arkorobotics/OneButton/Hardware/CAD/CAPC-0603-T0.9-BN.stp

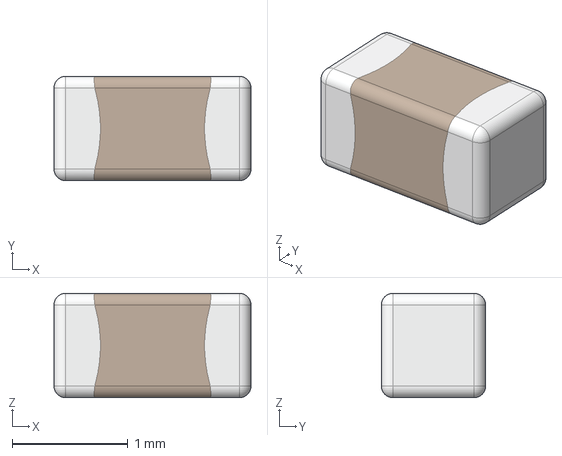
[picture p21: CAD file, 2017-11-20]
Hardware/CAD/CAPC-0603-T0.9-BN.stp
1.70 x 0.9 x 0.9 mm
