arkorobotics/OneButton/Hardware/CAD/MO-178AA.stp

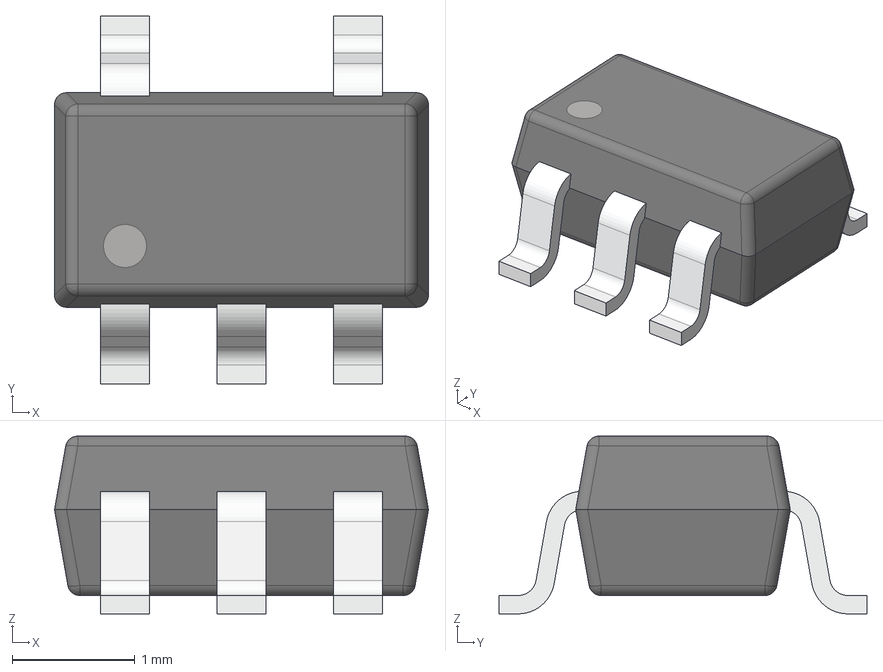
[picture p22: CAD file, 2017-11-20]
Hardware/CAD/MO-178AA.stp
3.05 x 3.00 x 1.45 mm
