arkorobotics/OneButton/Hardware/CAD/CAPC-1210-T1.8-BN.stp

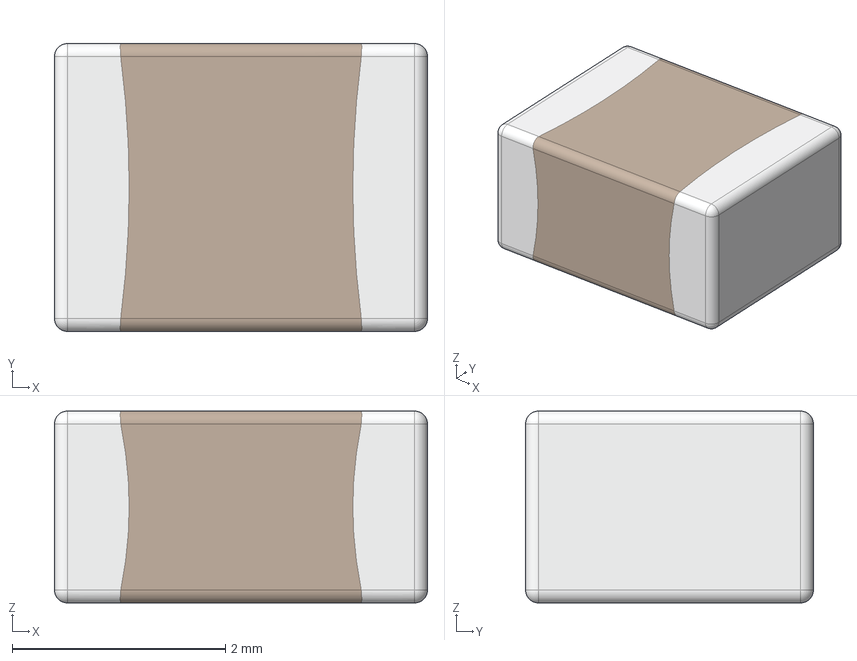
[picture p23: CAD file, 2017-11-20]
Hardware/CAD/CAPC-1210-T1.8-BN.stp
3.50 x 2.70 x 1.80 mm
