arkorobotics/OneButton/Hardware/CAD/SOT223.STEP

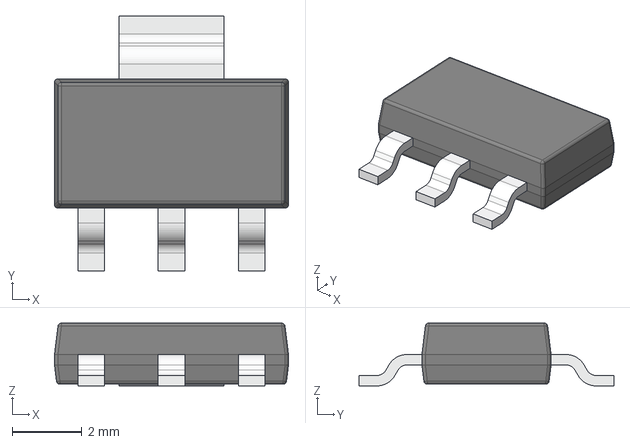
[picture p24: CAD file, 2017-11-20]
Hardware/CAD/SOT223.STEP
6.70 x 7.30 x 1.80 mm
