arkorobotics/OneButton/Hardware/CAD/SC-76.stp

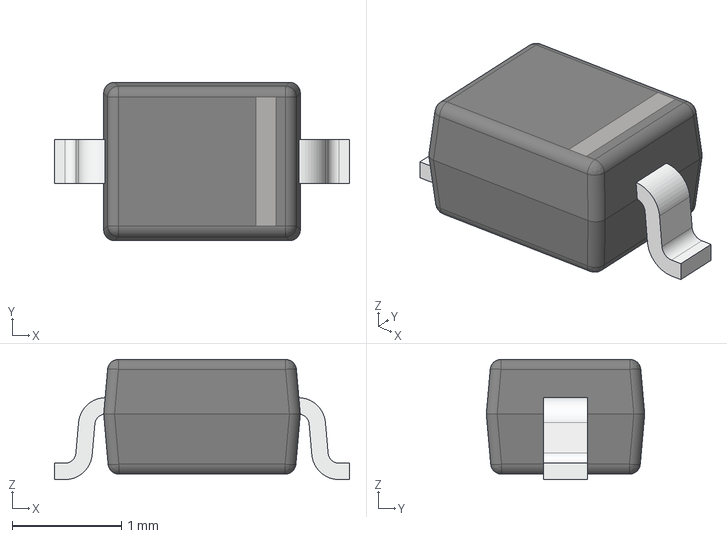
[picture p25: CAD file, 2017-11-20]
Hardware/CAD/SC-76.stp
2.70 x 1.45 x 1.10 mm
