arkorobotics/OneButton/Hardware/CAD/CAPC-1206-T1.8-BN.stp

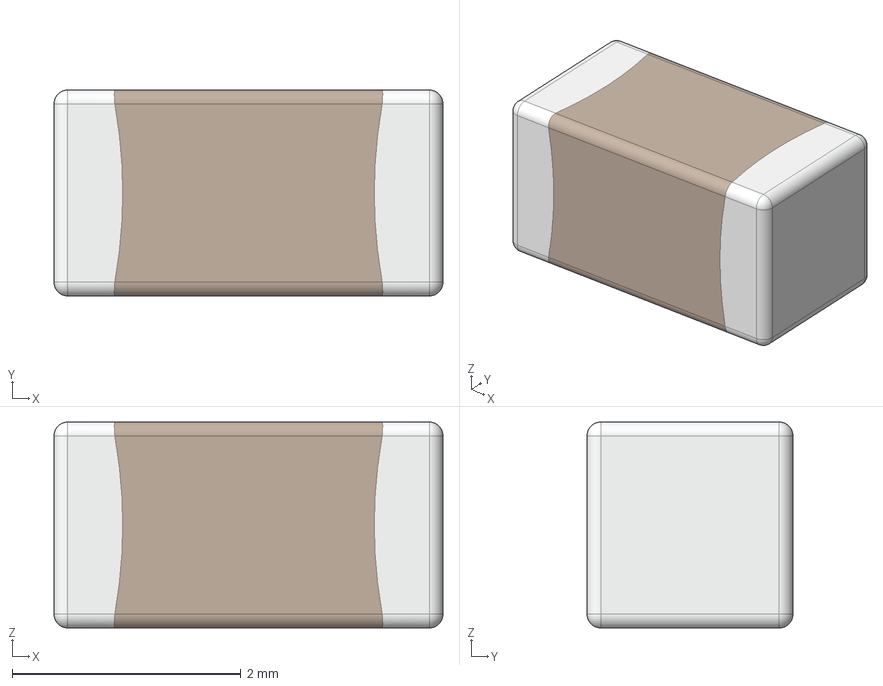
[picture p26: CAD file, 2017-11-20]
Hardware/CAD/CAPC-1206-T1.8-BN.stp
3.40 x 1.80 x 1.80 mm
