arkorobotics/OneButton/Hardware/CAD/Crystal.STEP

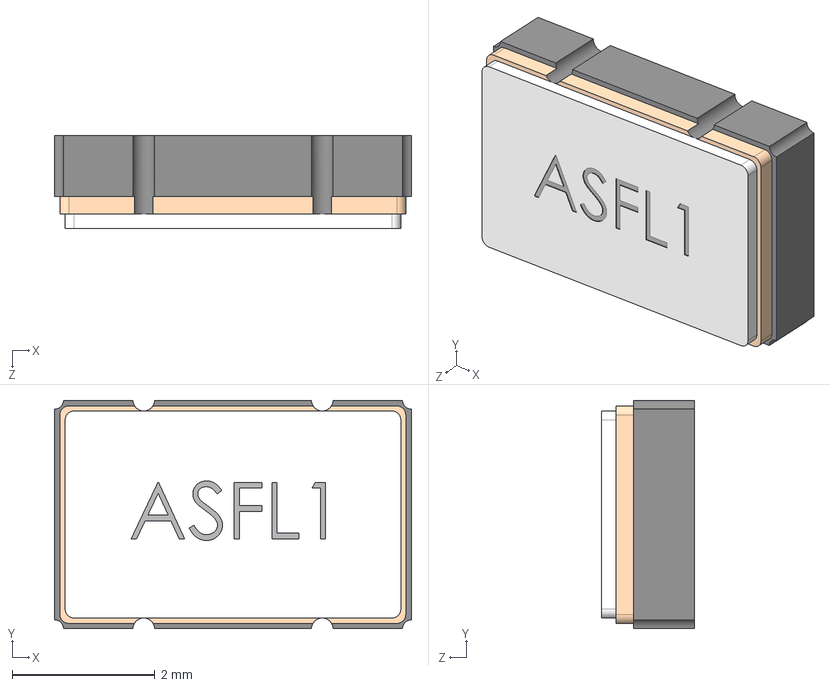
[picture p27: CAD file, 2017-11-20]
Hardware/CAD/Crystal.STEP
5.00 x 3.20 x 1.30 mm
