arkorobotics/OneButton/Hardware/CAD/UFQFPN28.STEP

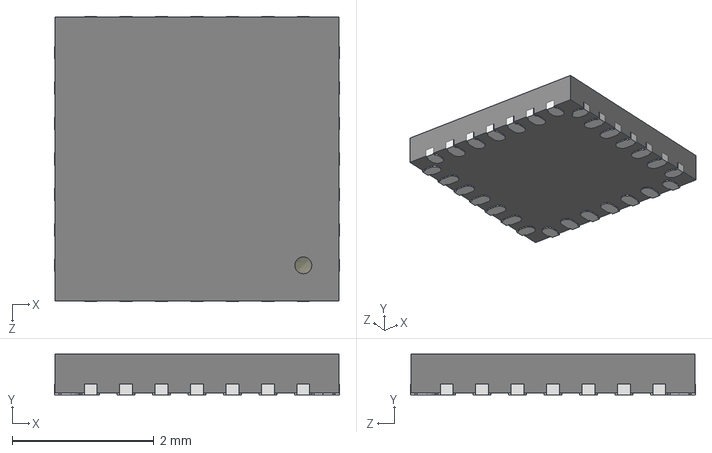
[picture p28: CAD file, 2017-11-20]
Hardware/CAD/UFQFPN28.STEP
4.02 x 0.575 x 4.02 mm
