arkorobotics/OneButton/Hardware/CAD/Tact_Switch.STEP

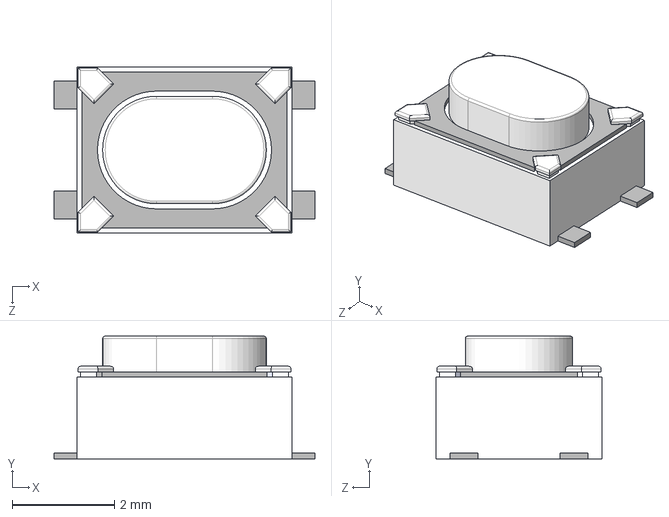
[picture p29: CAD file, 2017-11-20]
Hardware/CAD/Tact_Switch.STEP
5.10 x 2.40 x 3.25 mm
