arkorobotics/OneButton/Hardware/CAD/WS2812.stp

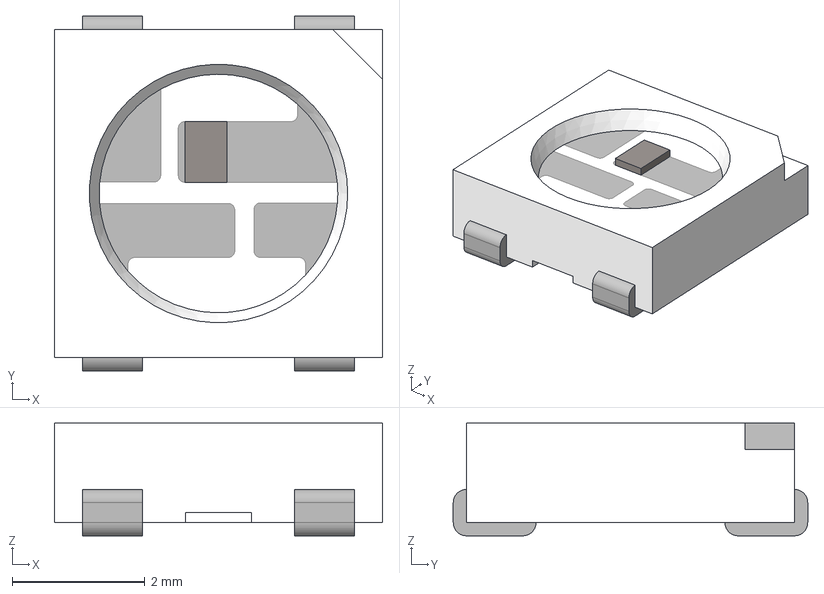
[picture p30: CAD file, 2017-11-20]
Hardware/CAD/WS2812.stp
4.95 x 5.35 x 1.70 mm
